and3rson/leo80/img/v1_io.jpg

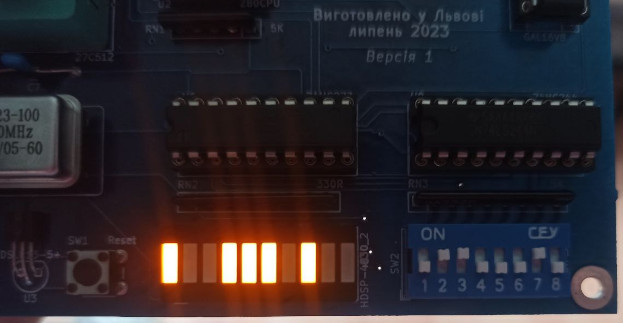
img/v1_io.jpg
