and3rson/leo80/img/v1_ioen.png

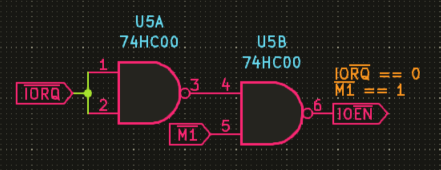
img/v1_ioen.png
