and3rson/leo80/img/v1a_bw.jpg

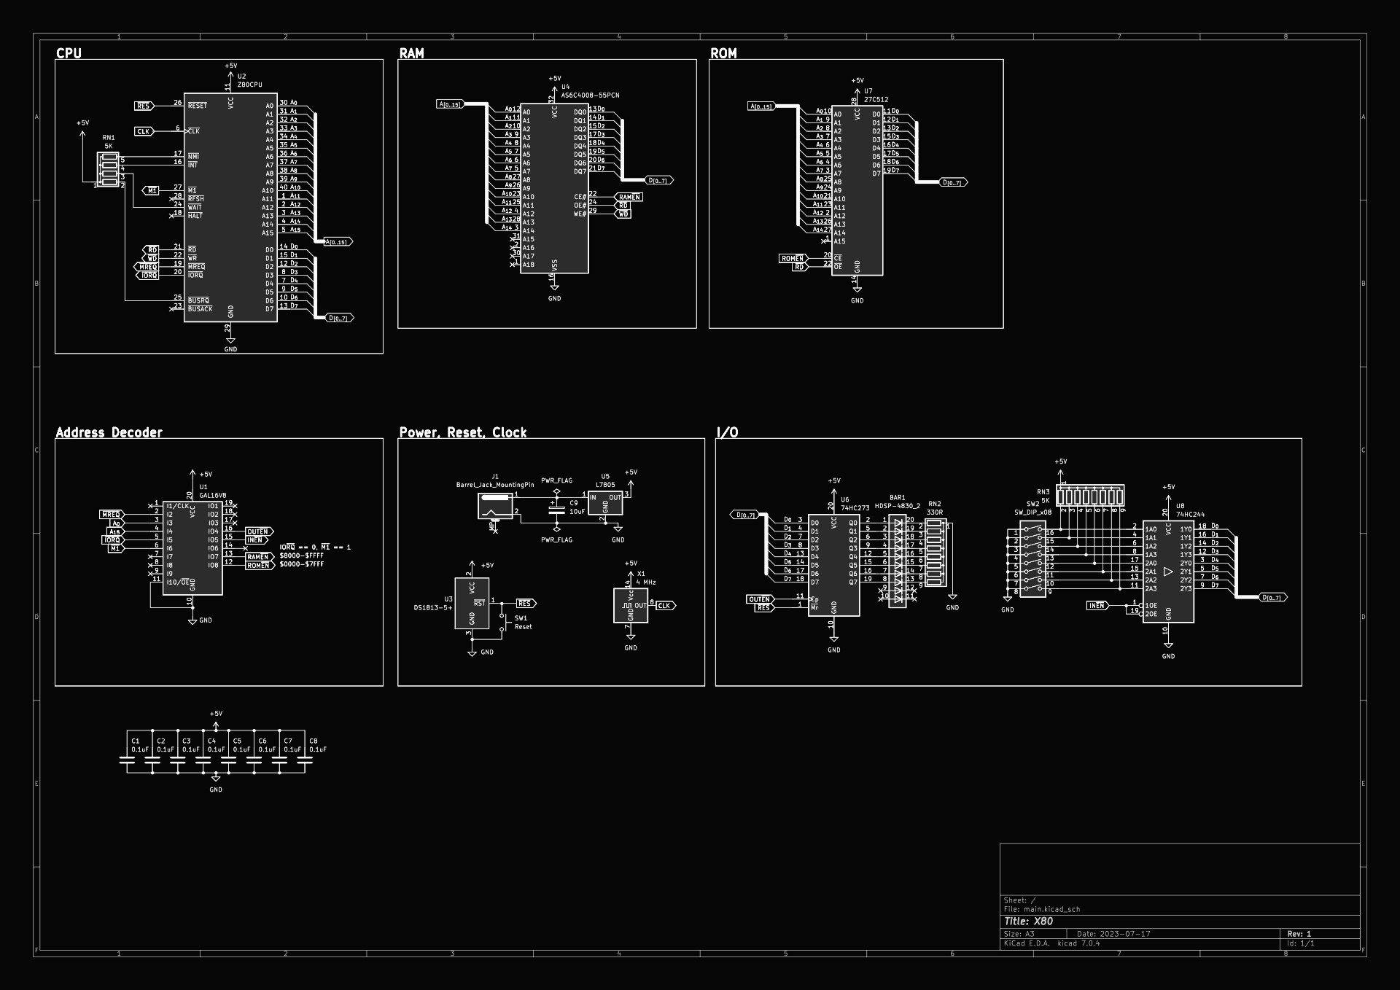
img/v1a_bw.jpg
