and3rson/leo80/img/v1_ram_issue1.jpg

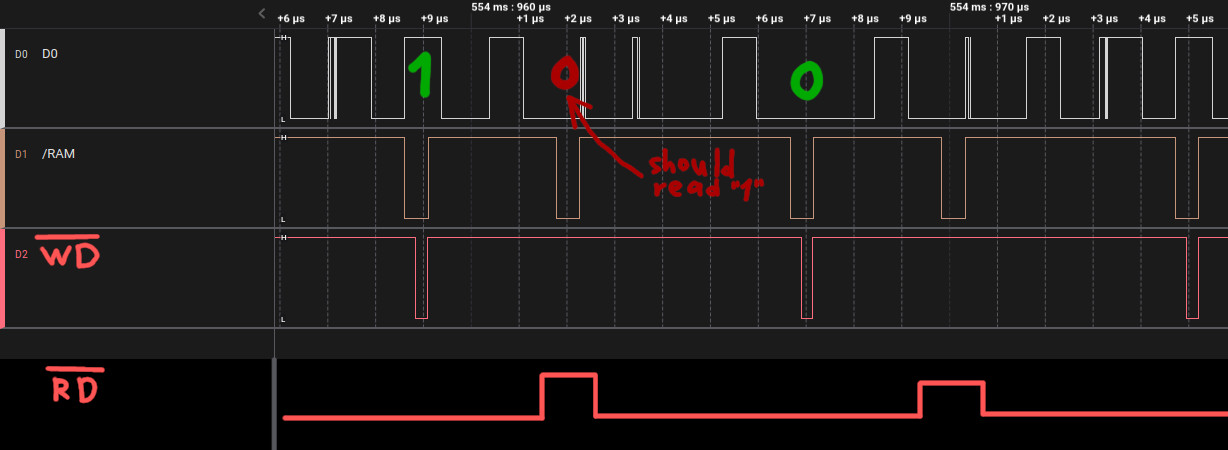
img/v1_ram_issue1.jpg
